Serggy10/15.-TFG-Thesis-Luminous-Road-Emergency-Panel/Entrega TFG/Presentacion TFG Panel Luminoso V2.pdf

PANEL LUMINOSO DE EMERGENCIA EN CARRETERA CONTROLADO POR PANTALLA TÁCTIL Y DE FORMA INALÁMBRICA SERGIO CARRASCO HERNÁNDEZ - IEIA

# PANEL LUMINOSO DE EMERGENCIA EN

# CARRETERA CONTROLADO POR PANTALLA

TÁCTIL Y DE FORMA INALÁMBRICA.

## Sergio Carrasco Hernández Grado en Ingeniería Electrónica Industrial y Automática

### Tutor: Luis Carlos Herrero de Lucas Departamento Tecnología Electrónica

### Universidad de Valladolid

POR PANTALLA TÁCTIL Y DE FORMA INALÁMBRICA SERGIO CARRASCO HERNÁNDEZ - IEIA

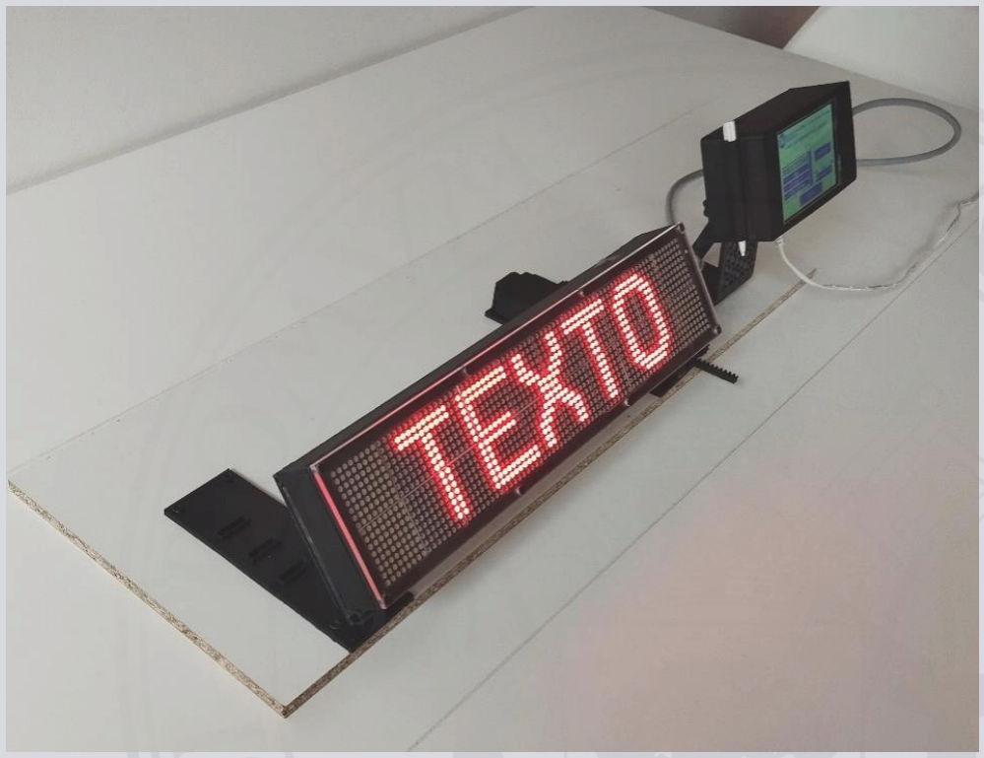
[picture p1: figure]

# ÍNDICE

1. ORIGEN DEL PROYECTO.
2. OBJETIVOS.
3. HARDWARE EMPLEADO.

# 4. PRUEBA DE LOS ELEMENTOS

5. FABRICACIÓN DEL PROTOTIPO.
6. PROGRAMACIÓN DEL PROTOTIPO.
7. RESUMEN DEL PROYECTO.
8. PLANES A FUTURO.

1. ORIGEN DEL PROYECTO.

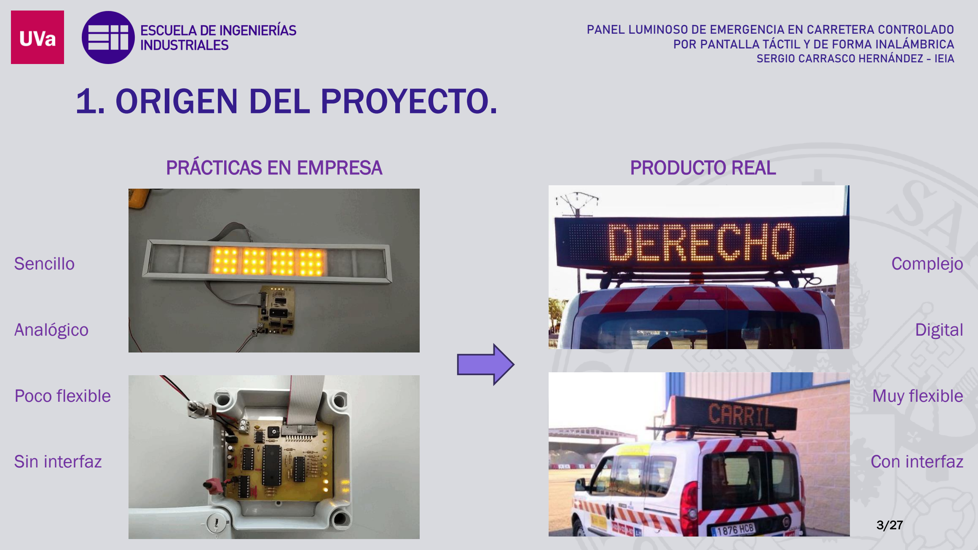
[picture p2: page 3]

POR PANTALLA TÁCTIL Y DE FORMA INALÁMBRICA SERGIO CARRASCO HERNÁNDEZ - IEIA

PRÁCTICAS EN EMPRESA | PRODUCTO REAL

## Sencillo

## Analógico

## Poco flexible

## Sin interfaz

## Complejo

## Digital

## Muy flexible

## Con interfaz

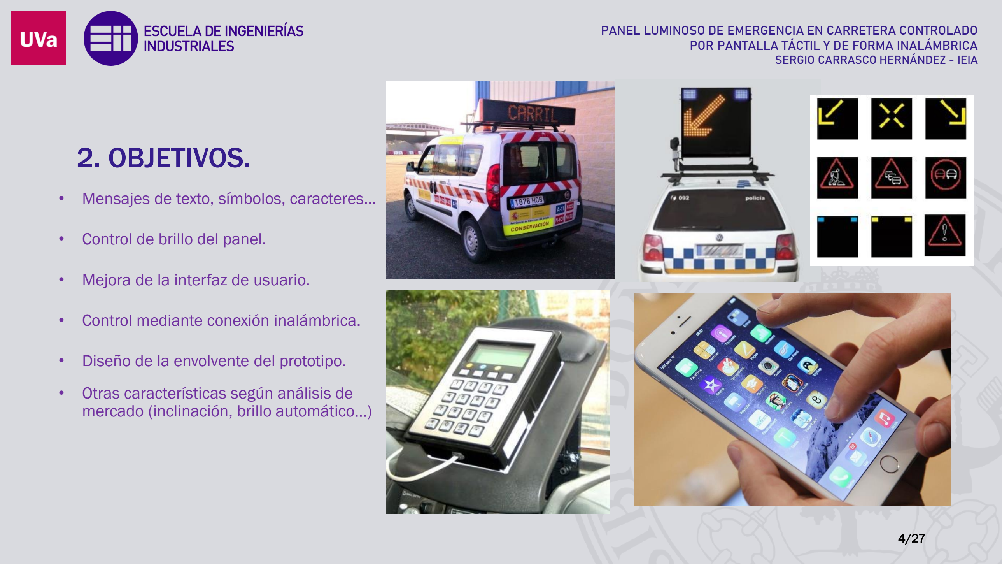
[picture p3: page 4]

POR PANTALLA TÁCTIL Y DE FORMA INALÁMBRICA SERGIO CARRASCO HERNÁNDEZ - IEIA

2. OBJETIVOS.
- Mensajes de texto, símbolos, caracteres…
- Control de brillo del panel.
- Mejora de la interfaz de usuario.
- Control mediante conexión inalámbrica.
- Diseño de la envolvente del prototipo.
- Otras características según análisis de mercado (inclinación, brillo automático…)

POR PANTALLA TÁCTIL Y DE FORMA INALÁMBRICA SERGIO CARRASCO HERNÁNDEZ - IEIA

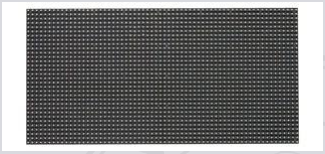
[picture p4: figure]

# 3. HARDWARE

EMPLEADO.

- 3.1. ALTERNATIVAS PARA EL PANEL LUMINOSO.

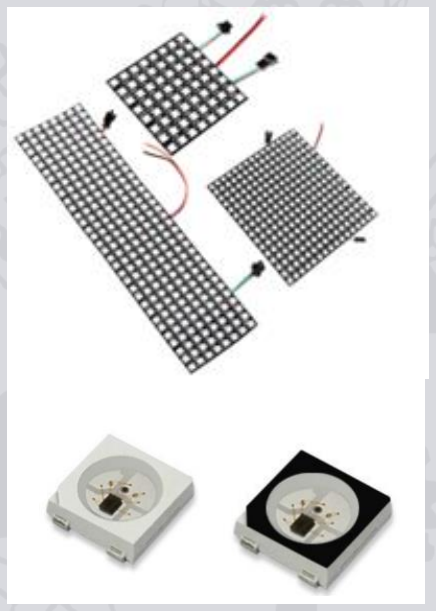
[picture p5: figure]

WS2812B | 5/27

LDM-6432

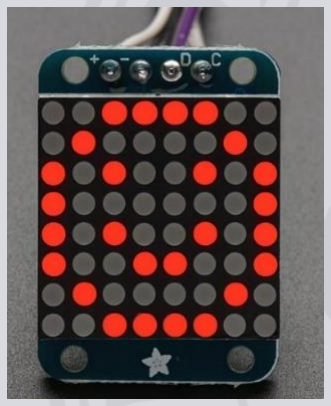
[picture p6: figure]

HT16K33
(I2C 8 DIRECCIONES)

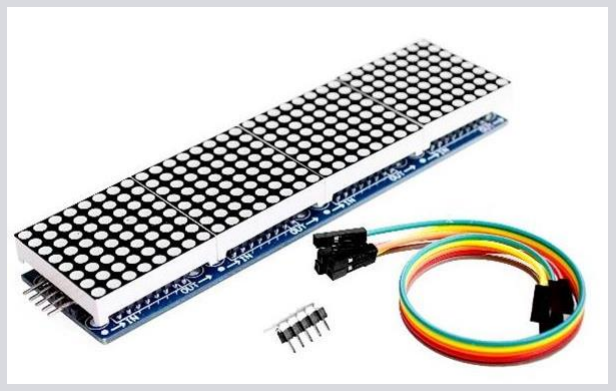
[picture p7: figure]

MAX7219/21
- Protocolo SPI.

## - Concatenación de multitud

de matrices.
- Memoria RAM.

## - Limitación de brillo de

forma externa.
- Alimentación a 5V.

# 3. HARDWARE

## PLACAS DE DESARROLLO

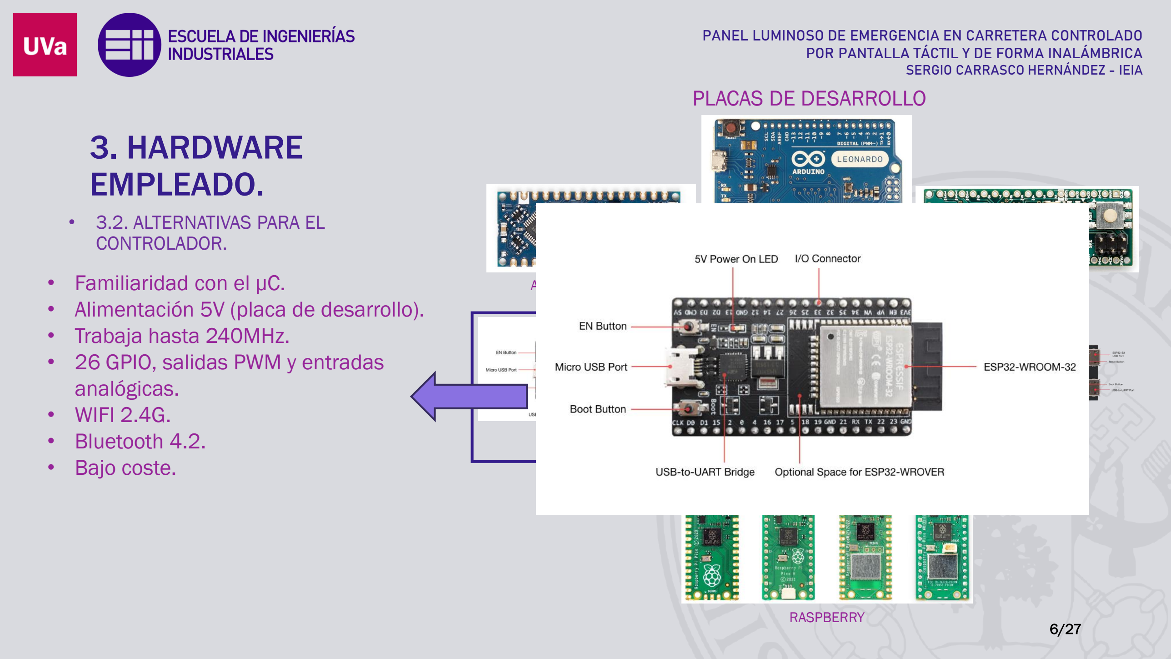
[picture p8: page 6]

POR PANTALLA TÁCTIL Y DE FORMA INALÁMBRICA SERGIO CARRASCO HERNÁNDEZ - IEIA

EMPLEADO.

- 3.2. ALTERNATIVAS PARA EL CONTROLADOR.
- Familiaridad con el µC.
- Alimentación 5V (placa de desarrollo).
- Trabaja hasta 240MHz.

## - 26 GPIO, salidas PWM y entradas

analógicas.
- WIFI 2.4G.
- Bluetooth 4.2.
- Bajo coste.

Arduino Nano Every
(ATMega4809)

Arduino Leonardo
(ATMega32u4)

Arduino Micro
(ATMega32u4)

ESP32 DEVKIT-C
(ESP32-WROOM)

ESP32-S2 DEVKIT-M-1
(ESP32-S2-MINI)

ESP32-S3-DEVKITC-1
(ESP32-S3-MINI)

RASPBERRY

POR PANTALLA TÁCTIL Y DE FORMA INALÁMBRICA SERGIO CARRASCO HERNÁNDEZ - IEIA

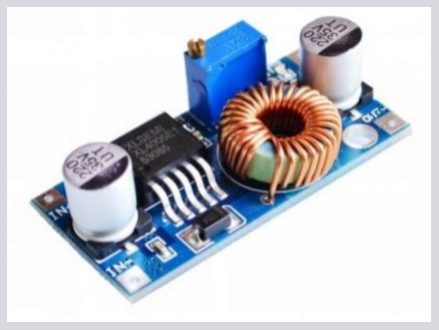
[picture p9: figure]

# 3. HARDWARE

EMPLEADO.

- 3.2. PERIFÉRICOS.

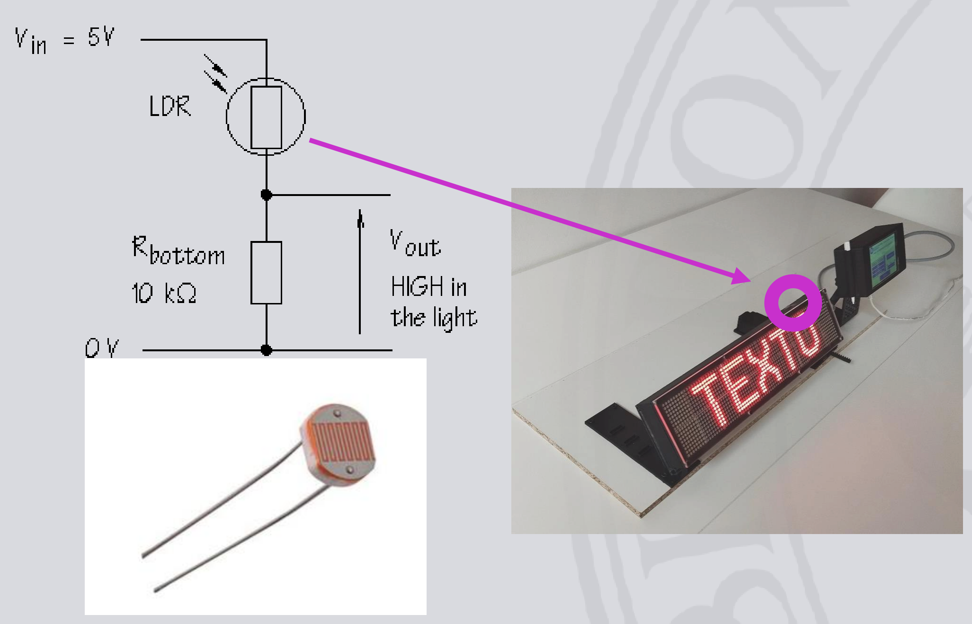
[picture p10: figure]
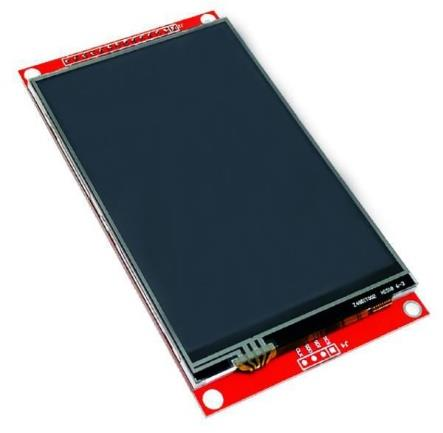
[picture p11: figure]
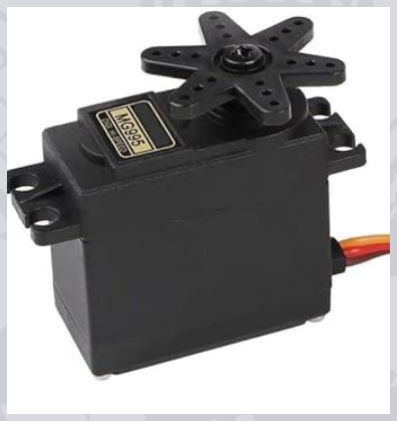
[picture p12: figure]

Pantalla táctil TFT SPI 480x320 píxeles | LDR | Servomotor MG995
INTERFAZ DE USUARIO | SENSOR DE NIVEL DE LUZ | SISTEMA PLEGADO

## ALIMENTACIÓN DEL DISPOSITVO

Convertidor CC-CC de 12V a 5V

# 4. PRUEBA DE LOS

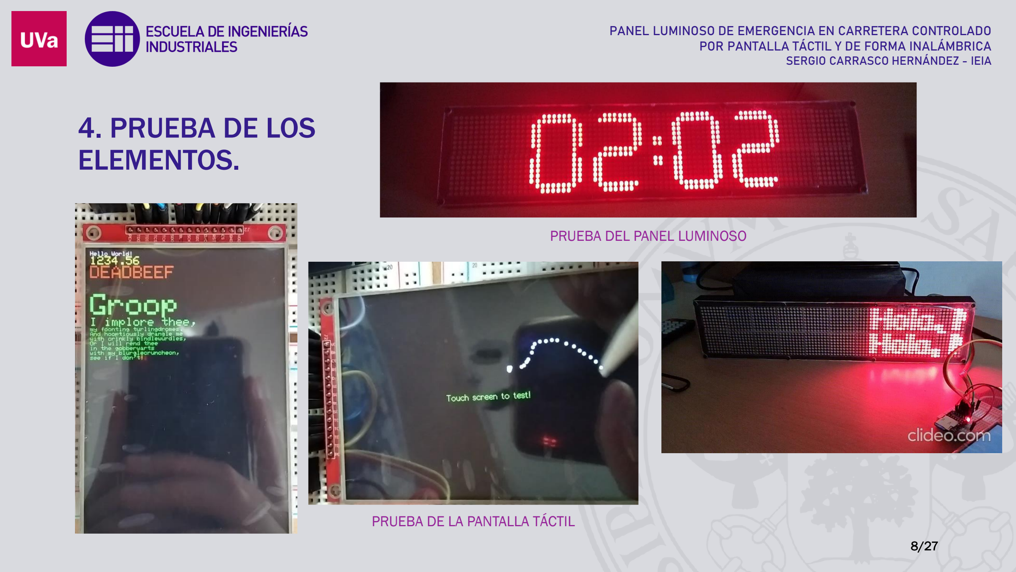
[picture p13: page 8]

POR PANTALLA TÁCTIL Y DE FORMA INALÁMBRICA SERGIO CARRASCO HERNÁNDEZ - IEIA

ELEMENTOS.

PRUEBA DEL PANEL LUMINOSO

PRUEBA DE LA PANTALLA TÁCTIL

# 5. FABRICACIÓN DEL

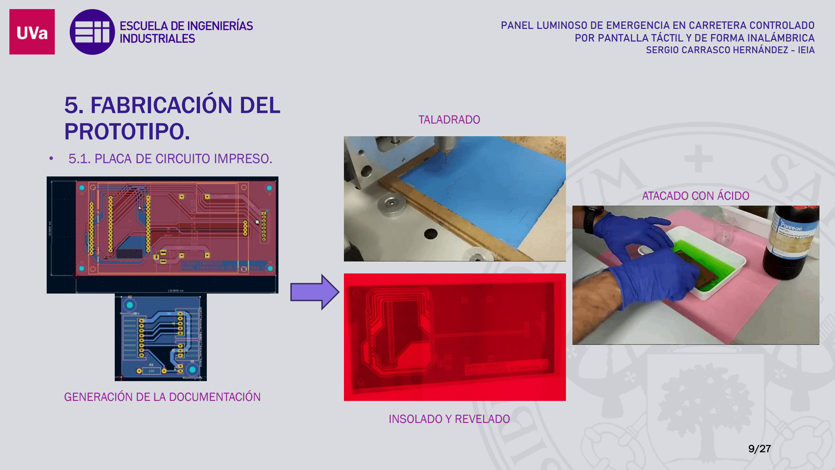
[picture p14: page 9]

POR PANTALLA TÁCTIL Y DE FORMA INALÁMBRICA SERGIO CARRASCO HERNÁNDEZ - IEIA

PROTOTIPO.

- 5.1. PLACA DE CIRCUITO IMPRESO.

GENERACIÓN DE LA DOCUMENTACIÓN

TALADRADO

INSOLADO Y REVELADO

ATACADO CON ÁCIDO

# 5. FABRICACIÓN DEL

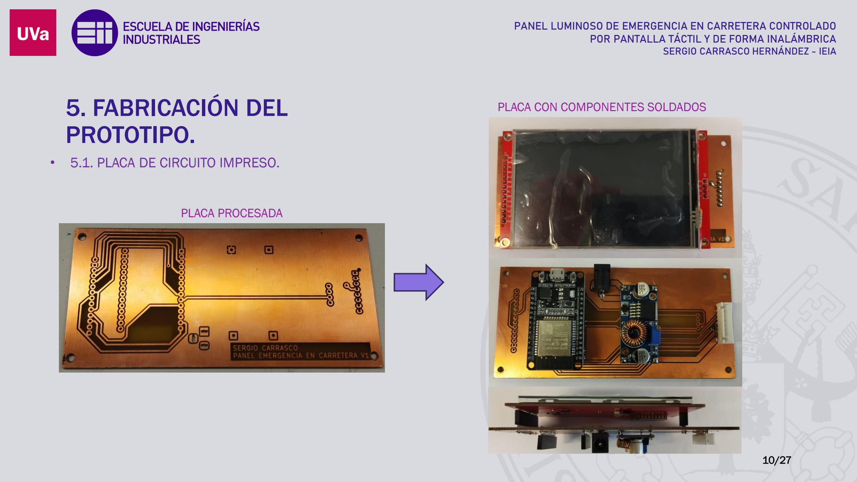
[picture p15: page 10]

POR PANTALLA TÁCTIL Y DE FORMA INALÁMBRICA SERGIO CARRASCO HERNÁNDEZ - IEIA

PROTOTIPO.

- 5.1. PLACA DE CIRCUITO IMPRESO.

PLACA PROCESADA

PLACA CON COMPONENTES SOLDADOS

# 5. FABRICACIÓN DEL

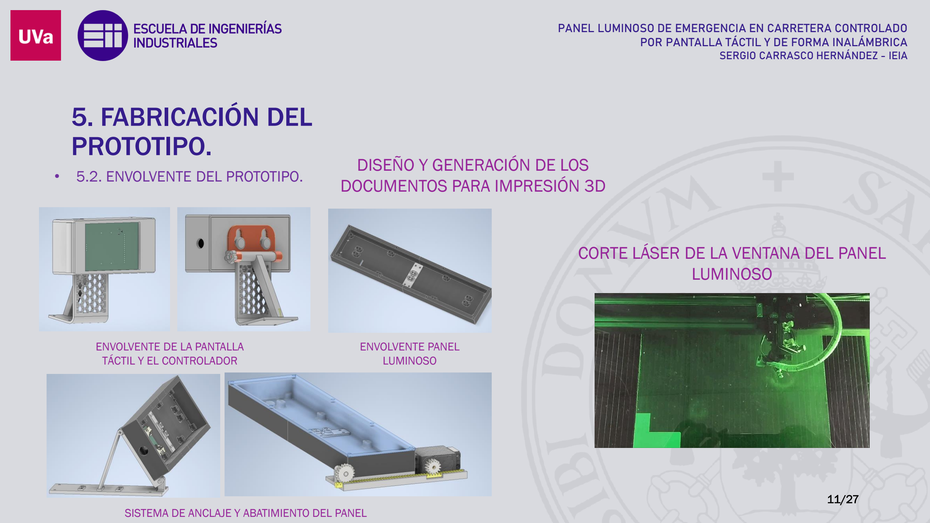
[picture p16: page 11]

POR PANTALLA TÁCTIL Y DE FORMA INALÁMBRICA SERGIO CARRASCO HERNÁNDEZ - IEIA

PROTOTIPO.

- 5.2. ENVOLVENTE DEL PROTOTIPO.

## DISEÑO Y GENERACIÓN DE LOS DOCUMENTOS PARA IMPRESIÓN 3D

ENVOLVENTE PANEL
LUMINOSO

ENVOLVENTE DE LA PANTALLA
TÁCTIL Y EL CONTROLADOR

SISTEMA DE ANCLAJE Y ABATIMIENTO DEL PANEL

## CORTE LÁSER DE LA VENTANA DEL PANEL LUMINOSO

# 5. FABRICACIÓN DEL

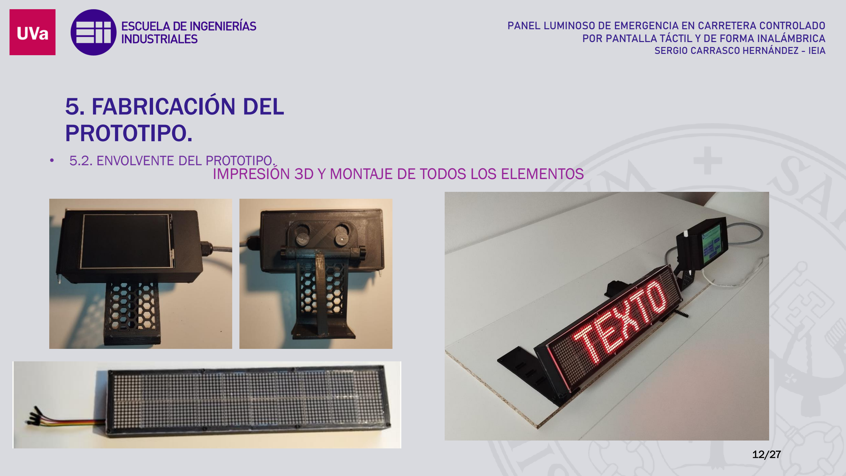
[picture p17: page 12]

POR PANTALLA TÁCTIL Y DE FORMA INALÁMBRICA SERGIO CARRASCO HERNÁNDEZ - IEIA

PROTOTIPO.

- 5.2. ENVOLVENTE DEL PROTOTIPO.

## IMPRESIÓN 3D Y MONTAJE DE TODOS LOS ELEMENTOS

POR PANTALLA TÁCTIL Y DE FORMA INALÁMBRICA SERGIO CARRASCO HERNÁNDEZ - IEIA

# 6. PROGRAMACIÓN DEL PROTOTIPO

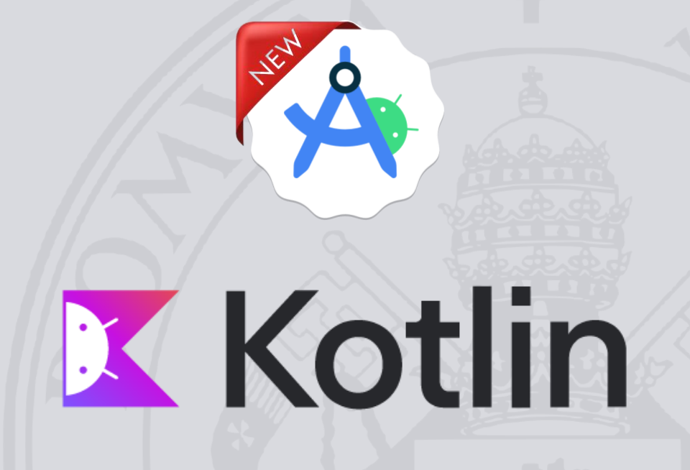
[picture p18: figure]
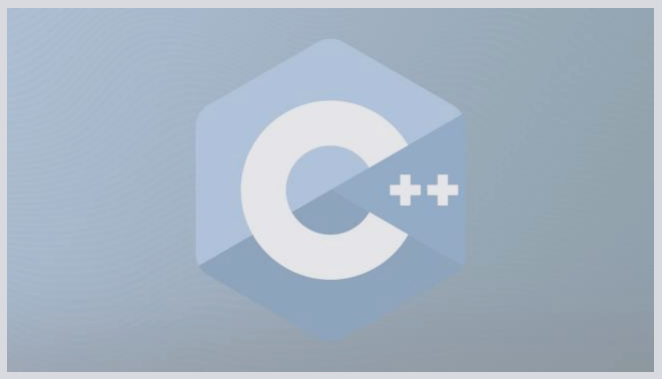
[picture p19: figure]

# 6. PROGRAMACIÓN DEL

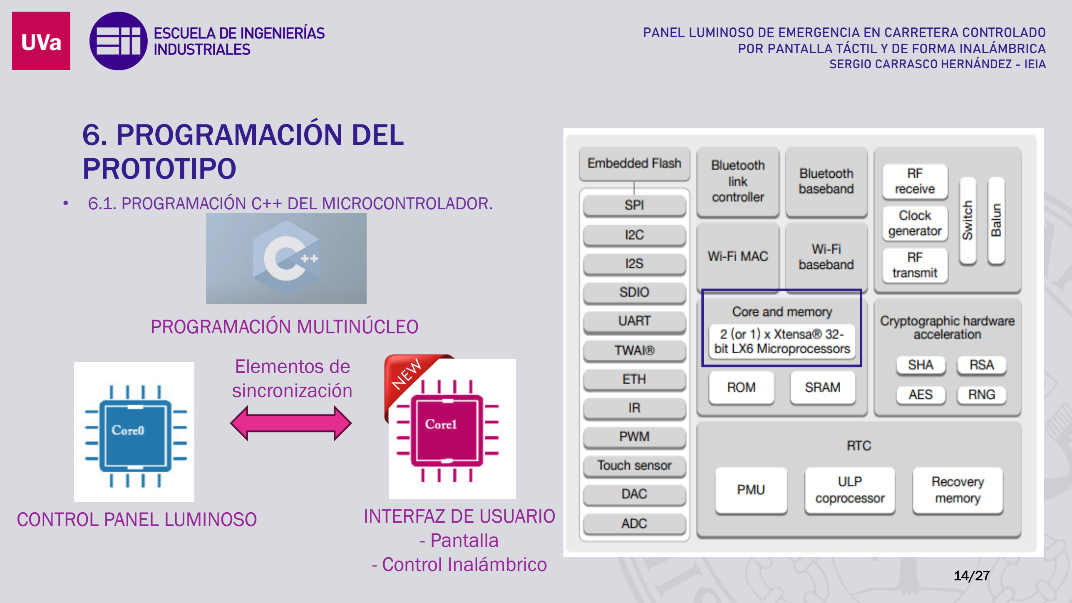
[picture p20: page 14]

POR PANTALLA TÁCTIL Y DE FORMA INALÁMBRICA SERGIO CARRASCO HERNÁNDEZ - IEIA

# PROTOTIPO

- 6.1. PROGRAMACIÓN C++ DEL MICROCONTROLADOR.

## PROGRAMACIÓN MULTINÚCLEO

CONTROL PANEL LUMINOSO | INTERFAZ DE USUARIO

## - Pantalla - Control Inalámbrico

## Elementos de sincronización

POR PANTALLA TÁCTIL Y DE FORMA INALÁMBRICA SERGIO CARRASCO HERNÁNDEZ - IEIA

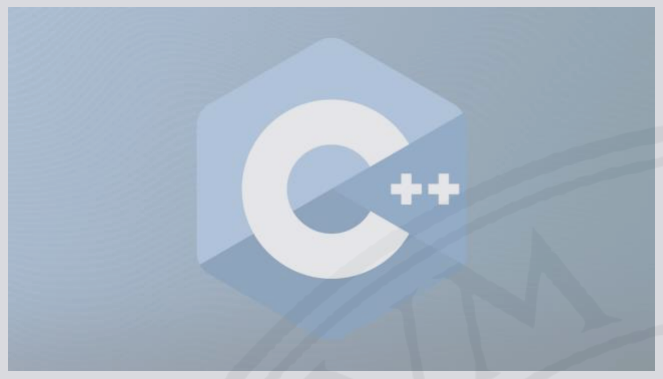
[picture p21: figure]

# 6. PROGRAMACIÓN DEL

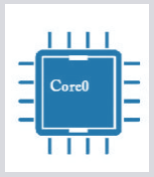
[picture p22: figure]

# PROTOTIPO

- 6.1. PROGRAMACIÓN C++ DEL MICROCONTROLADOR.

## NÚCLEO 0: PANEL LUMINOSO

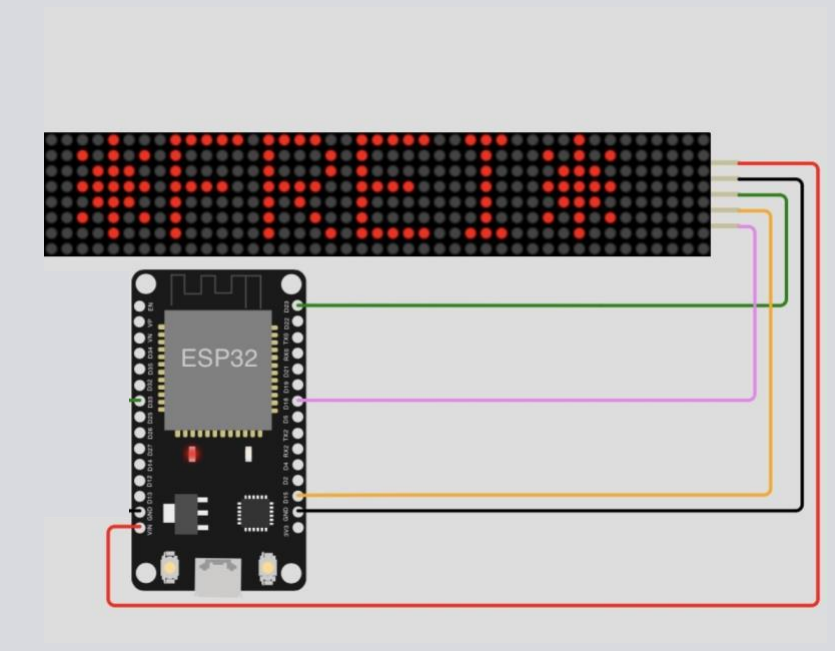
[picture p23: figure]

- Creación de librerías propias y modificación de las existentes.
- Creación de fuentes y caracteres especiales.
- Inclinación del panel mediante un servomotor.
- Ajuste automático del nivel de brillo mediante LDR.
- Guardado de parámetros de inclinación y brillo en SPIFFS.
- La gestión de los mensajes mediante máquina de estados.

# 6. PROGRAMACIÓN DEL

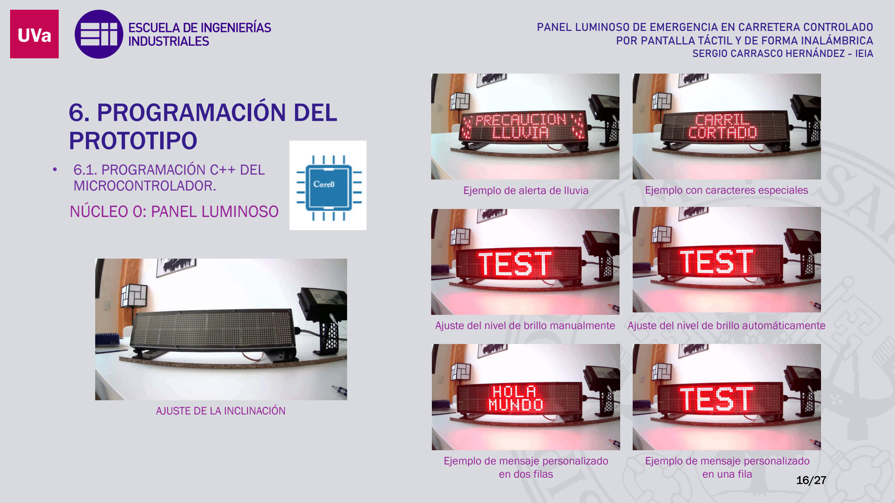
[picture p24: page 16]

POR PANTALLA TÁCTIL Y DE FORMA INALÁMBRICA SERGIO CARRASCO HERNÁNDEZ - IEIA

# PROTOTIPO

- 6.1. PROGRAMACIÓN C++ DEL MICROCONTROLADOR.

## NÚCLEO 0: PANEL LUMINOSO

AJUSTE DE LA INCLINACIÓN

Ajuste del nivel de brillo manualmente | Ajuste del nivel de brillo automáticamente
Ejemplo de alerta de lluvia | Ejemplo con caracteres especiales

Ejemplo de mensaje personalizado en dos filas

Ejemplo de mensaje personalizado en una fila

# 6. PROGRAMACIÓN DEL

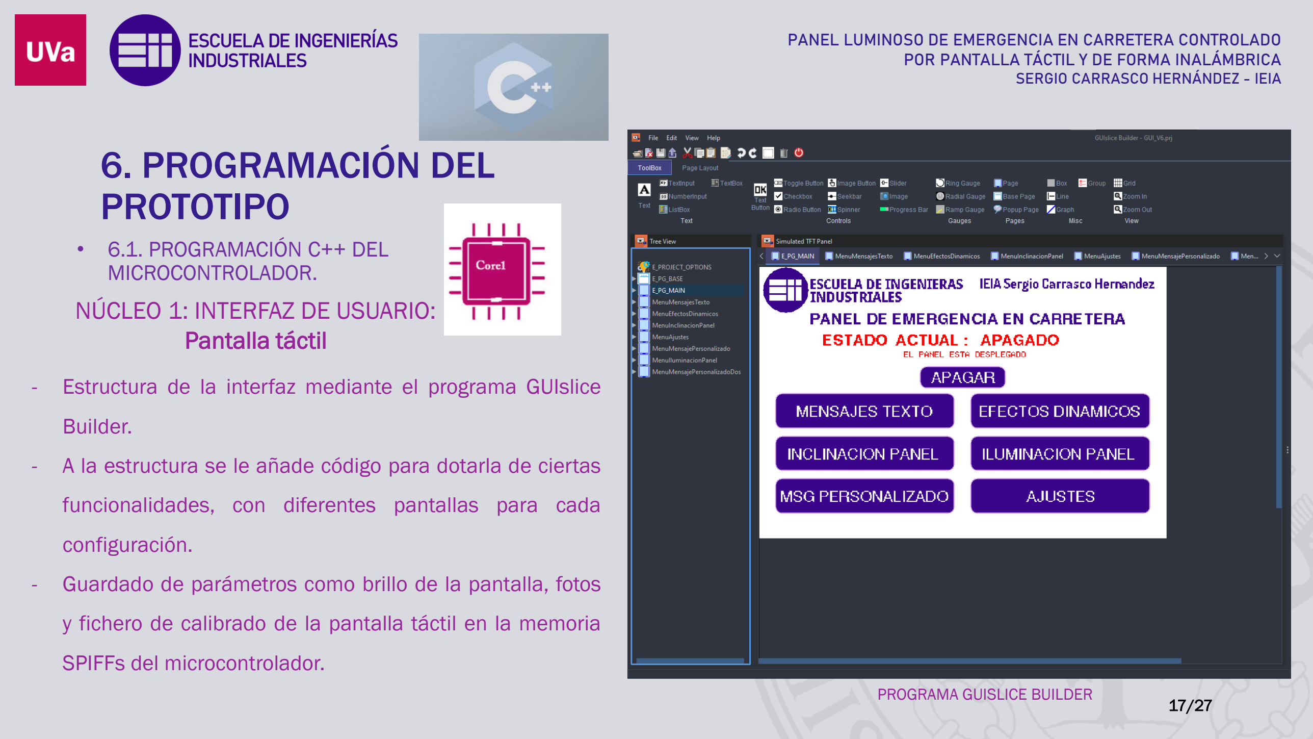
[picture p25: page 17]

POR PANTALLA TÁCTIL Y DE FORMA INALÁMBRICA SERGIO CARRASCO HERNÁNDEZ - IEIA

# PROTOTIPO

- 6.1. PROGRAMACIÓN C++ DEL MICROCONTROLADOR.

## NÚCLEO 1: INTERFAZ DE USUARIO: Pantalla táctil

PROGRAMA GUISLICE BUILDER

- Estructura de la interfaz mediante el programa GUIslice

Builder.

- A la estructura se le añade código para dotarla de ciertas

funcionalidades, con diferentes pantallas para cada

configuración.

- Guardado de parámetros como brillo de la pantalla, fotos

y fichero de calibrado de la pantalla táctil en la memoria

SPIFFs del microcontrolador.

# 6. PROGRAMACIÓN DEL

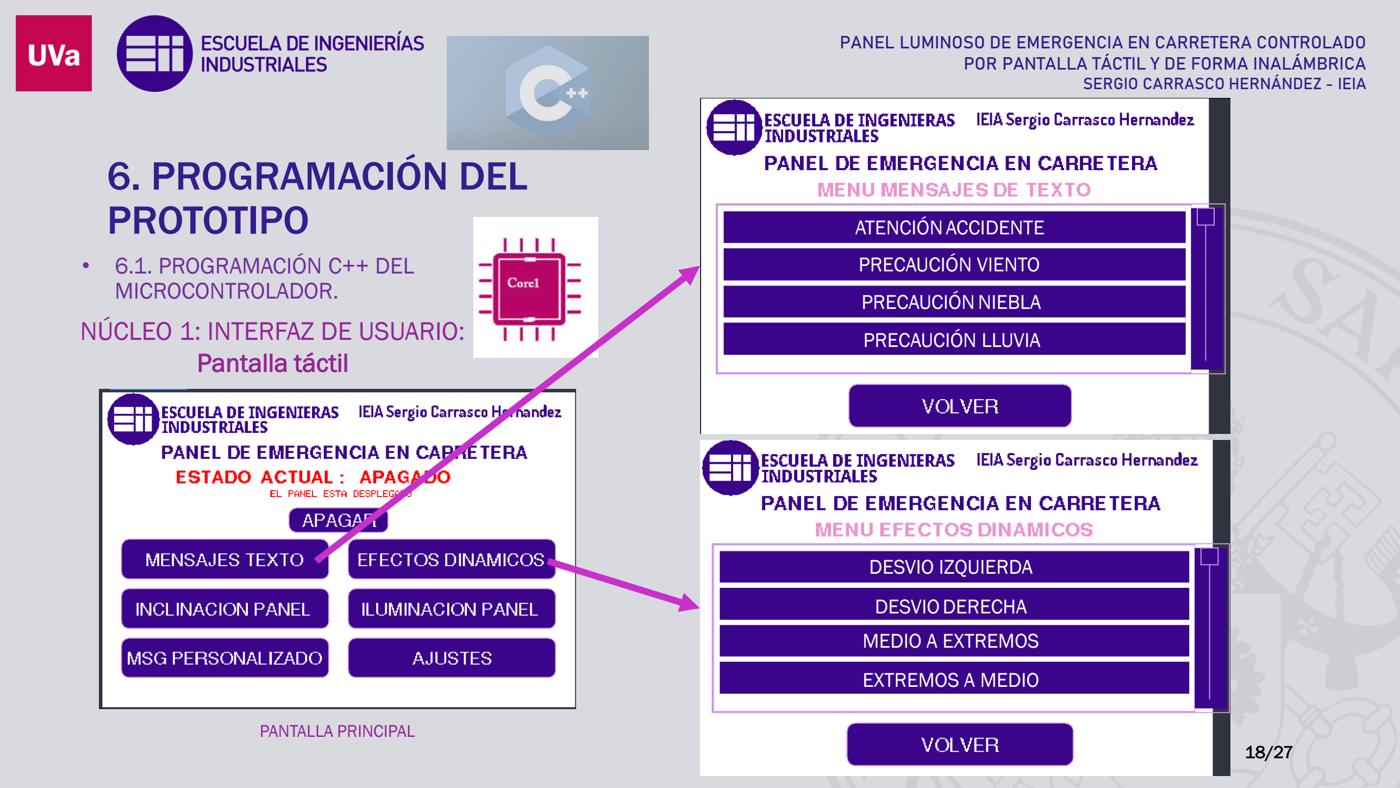
[picture p26: page 18]

POR PANTALLA TÁCTIL Y DE FORMA INALÁMBRICA SERGIO CARRASCO HERNÁNDEZ - IEIA

# PROTOTIPO

- 6.1. PROGRAMACIÓN C++ DEL MICROCONTROLADOR.

## NÚCLEO 1: INTERFAZ DE USUARIO: Pantalla táctil

PANTALLA PRINCIPAL

ATENCIÓNACCIDENTE

PRECAUCIÓN VIENTO

PRECAUCIÓNNIEBLA

PRECAUCIÓN LLUVIA

DESVIO IZQUIERDA

DESVIODERECHA

MEDIO A EXTREMOS

EXTREMOS A MEDIO

# 6. PROGRAMACIÓN DEL

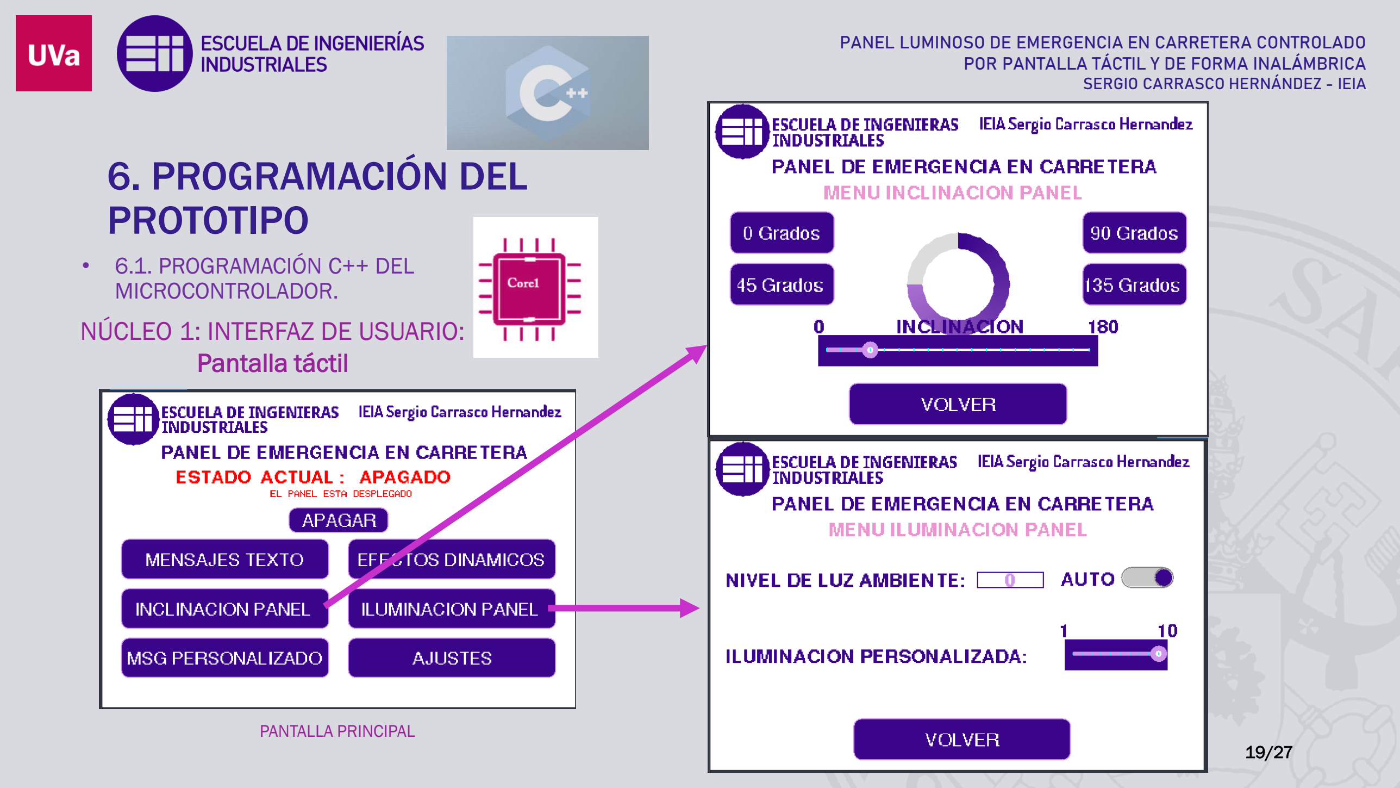
[picture p27: page 19]

POR PANTALLA TÁCTIL Y DE FORMA INALÁMBRICA SERGIO CARRASCO HERNÁNDEZ - IEIA

# PROTOTIPO

- 6.1. PROGRAMACIÓN C++ DEL MICROCONTROLADOR.

## NÚCLEO 1: INTERFAZ DE USUARIO: Pantalla táctil

PANTALLA PRINCIPAL

# 6. PROGRAMACIÓN DEL

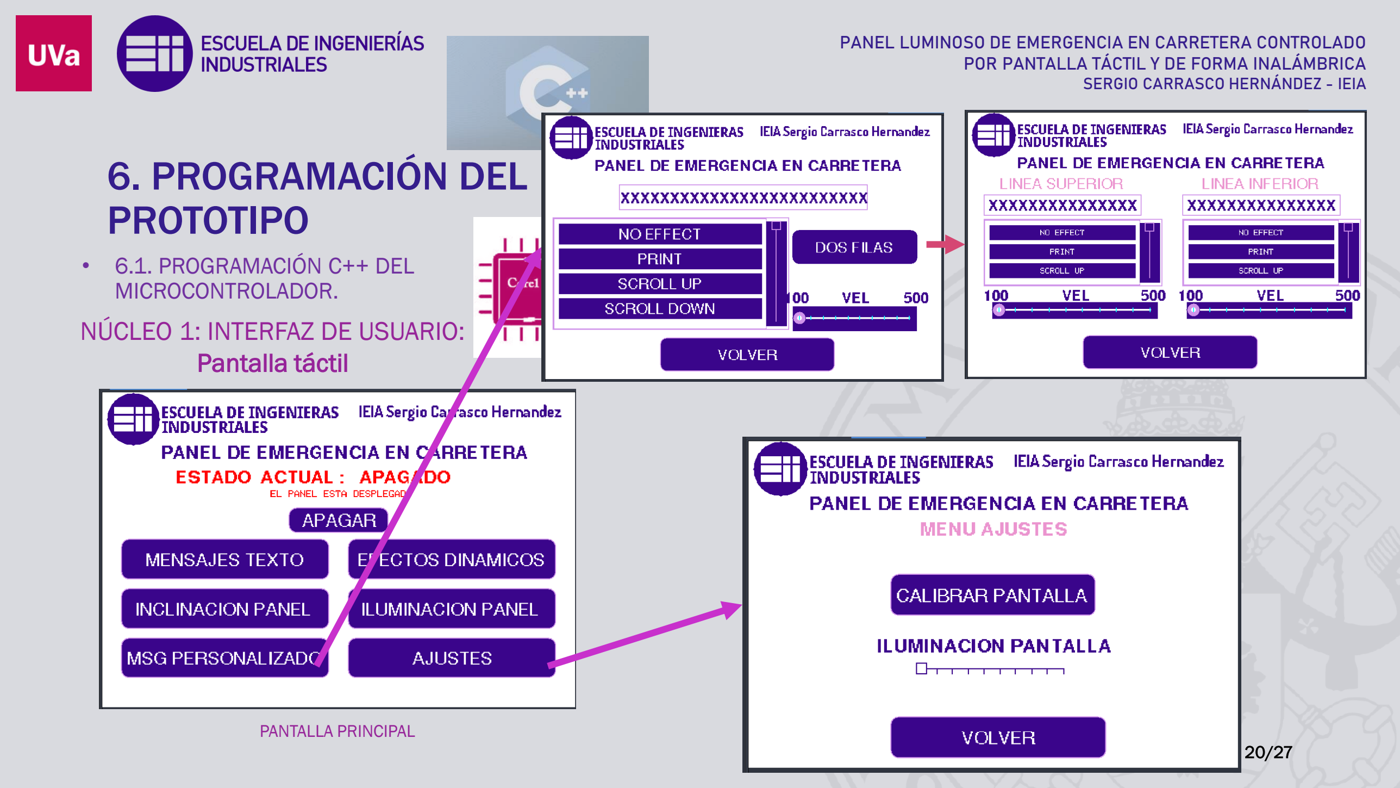
[picture p28: page 20]

POR PANTALLA TÁCTIL Y DE FORMA INALÁMBRICA SERGIO CARRASCO HERNÁNDEZ - IEIA

# PROTOTIPO

- 6.1. PROGRAMACIÓN C++ DEL MICROCONTROLADOR.

## NÚCLEO 1: INTERFAZ DE USUARIO: Pantalla táctil

PANTALLA PRINCIPAL

# 6. PROGRAMACIÓN DEL

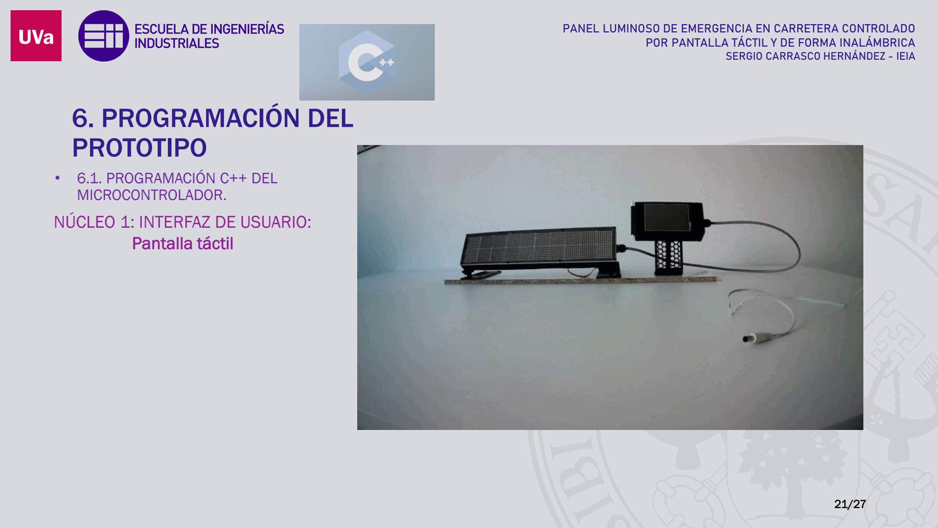
[picture p29: page 21]

POR PANTALLA TÁCTIL Y DE FORMA INALÁMBRICA SERGIO CARRASCO HERNÁNDEZ - IEIA

# PROTOTIPO

- 6.1. PROGRAMACIÓN C++ DEL MICROCONTROLADOR.

## NÚCLEO 1: INTERFAZ DE USUARIO: Pantalla táctil

Video

# 6. PROGRAMACIÓN DEL

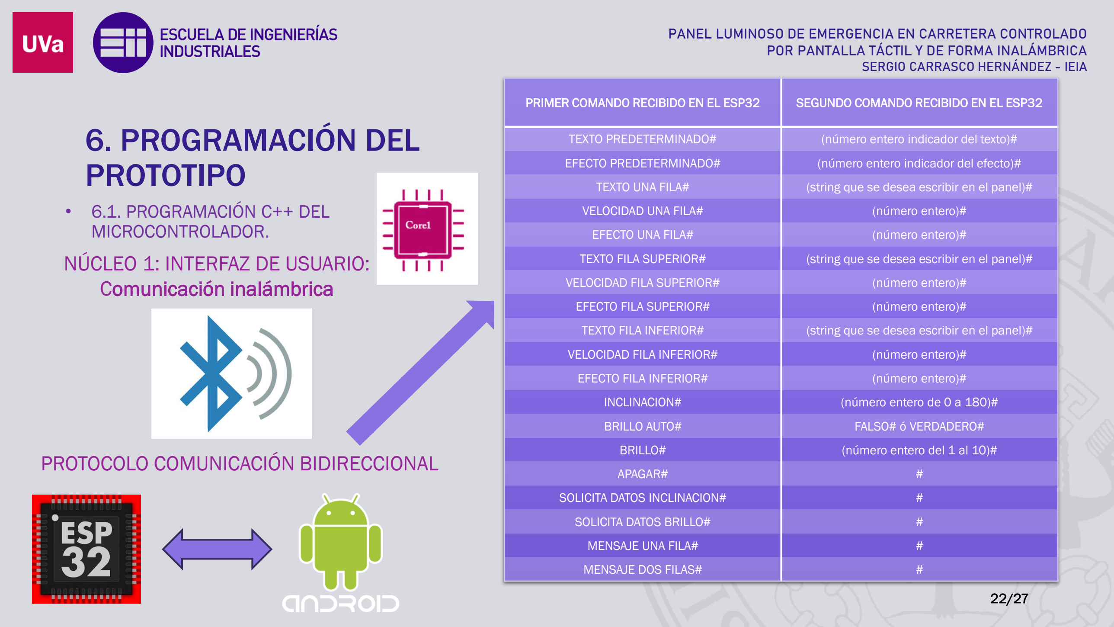
[picture p30: page 22]

POR PANTALLA TÁCTIL Y DE FORMA INALÁMBRICA SERGIO CARRASCO HERNÁNDEZ - IEIA

PRIMER COMANDO RECIBIDO EN EL ESP32 | SEGUNDO COMANDO RECIBIDO EN EL ESP32
TEXTO PREDETERMINADO# | (número entero indicador del texto)#
EFECTO PREDETERMINADO# | (número entero indicador del efecto)#
TEXTO UNA FILA# | (string que se desea escribir en el panel)#
VELOCIDAD UNA FILA# | (número entero)#
EFECTO UNA FILA# | (número entero)#
TEXTO FILA SUPERIOR# | (string que se desea escribir en el panel)#
VELOCIDAD FILA SUPERIOR# | (número entero)#
EFECTO FILA SUPERIOR# | (número entero)#
TEXTO FILA INFERIOR# | (string que se desea escribir en el panel)#
VELOCIDAD FILA INFERIOR# | (número entero)#
EFECTO FILA INFERIOR# | (número entero)#
INCLINACION# | (número entero de 0 a 180)#
BRILLO AUTO# | FALSO# ó VERDADERO#
BRILLO# | (número entero del 1 al 10)#
APAGAR# | #
SOLICITA DATOS INCLINACION# | #
SOLICITA DATOS BRILLO# | #
MENSAJE UNA FILA# | #
MENSAJE DOS FILAS# | #

# PROTOTIPO

- 6.1. PROGRAMACIÓN C++ DEL MICROCONTROLADOR.

## NÚCLEO 1: INTERFAZ DE USUARIO: Comunicación inalámbrica

## PROTOCOLO COMUNICACIÓN BIDIRECCIONAL

# 6. PROGRAMACIÓN DEL

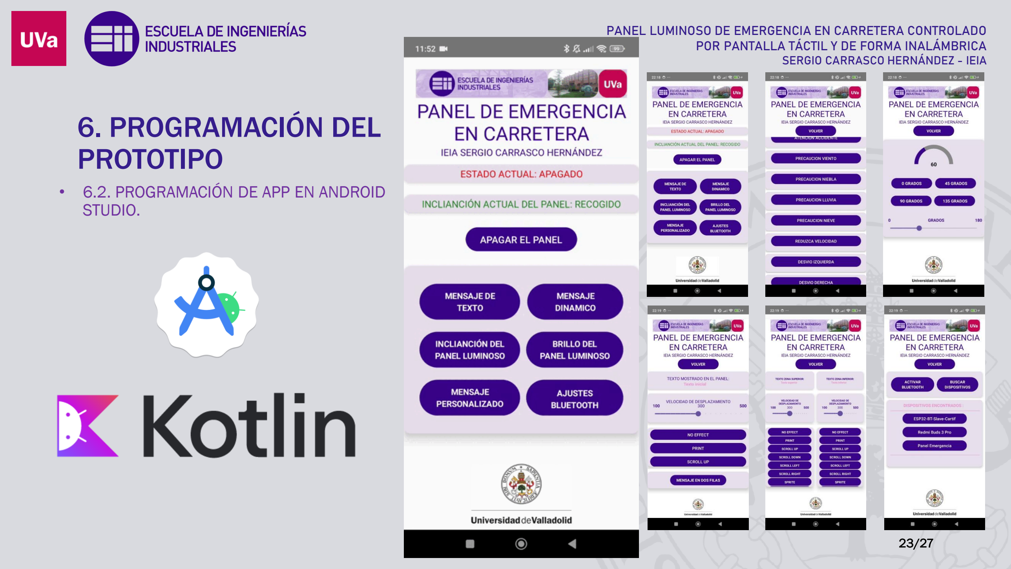
[picture p31: page 23]

POR PANTALLA TÁCTIL Y DE FORMA INALÁMBRICA SERGIO CARRASCO HERNÁNDEZ - IEIA

# PROTOTIPO

- 6.2. PROGRAMACIÓN DE APP EN ANDROID STUDIO.

# 6. PROGRAMACIÓN DEL

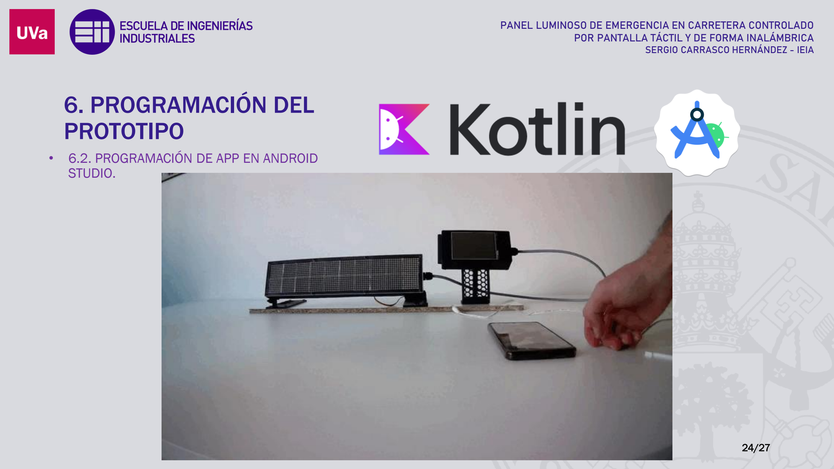
[picture p32: page 24]

POR PANTALLA TÁCTIL Y DE FORMA INALÁMBRICA SERGIO CARRASCO HERNÁNDEZ - IEIA

# PROTOTIPO

- 6.2. PROGRAMACIÓN DE APP EN ANDROID STUDIO.

POR PANTALLA TÁCTIL Y DE FORMA INALÁMBRICA SERGIO CARRASCO HERNÁNDEZ - IEIA

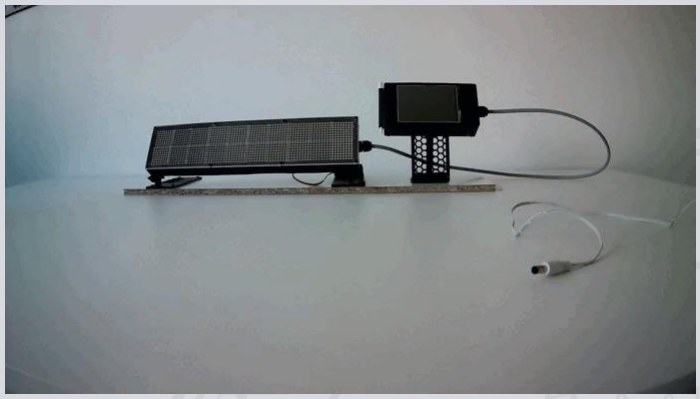
[picture p33: figure]

# 7. RESUMEN DEL

PROYECTO.

✓ Cumplimiento de objetivos:

✓ | Mensajes de texto.
✓ | Mensajes más complejos.
✓ | Mejora de la interfaz de usuario.
✓ | Control de luminosidad.
✓ | Panel plegable.
✓ | Comunicación inalámbrica por Bluetooth.

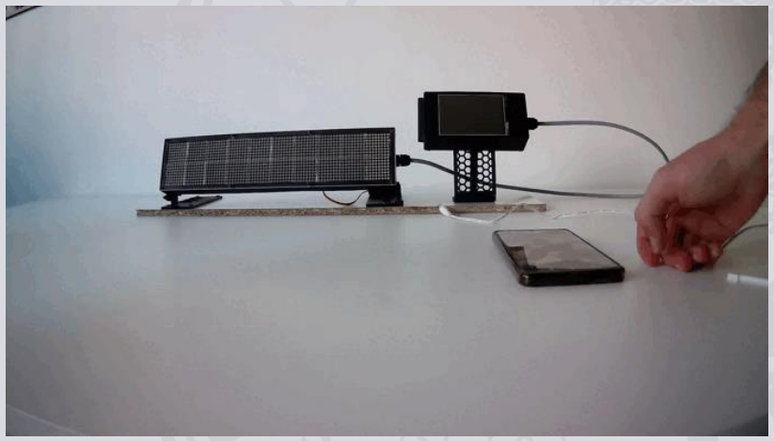
[picture p34: figure]

✓ Diseño y fabricación de la PCB.

✓ Diseño y fabricación de la envolvente.

✓ Programación multinúcleo.

✓ Programación de una aplicación Android desde cero.

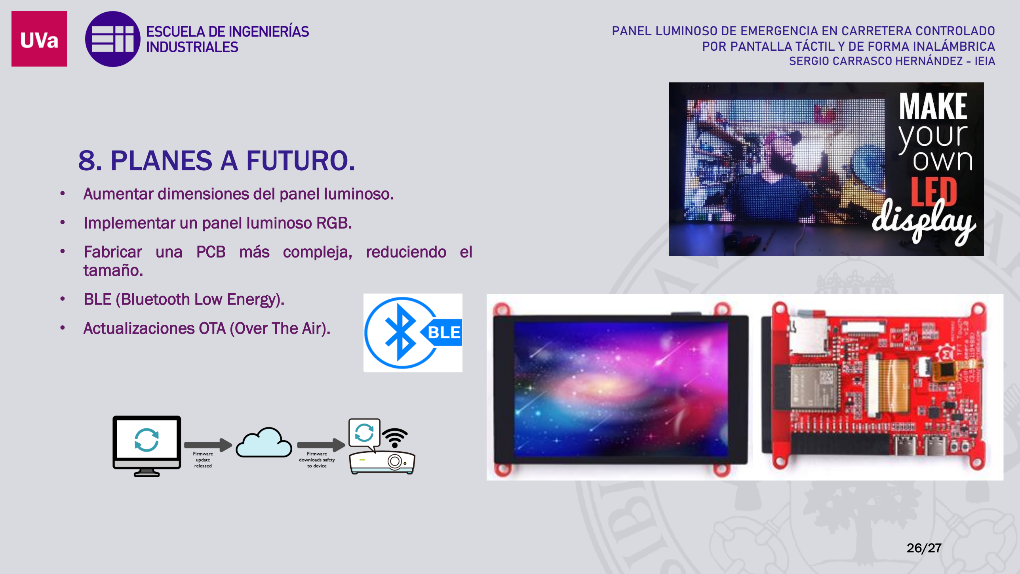
[picture p35: page 26]

POR PANTALLA TÁCTIL Y DE FORMA INALÁMBRICA SERGIO CARRASCO HERNÁNDEZ - IEIA

8. PLANES A FUTURO.
- Aumentar dimensiones del panel luminoso.
- Implementar un panel luminoso RGB.
- Fabricar una PCB más compleja, reduciendo el tamaño.
- BLE (Bluetooth Low Energy).
- Actualizaciones OTA (Over The Air).

POR PANTALLA TÁCTIL Y DE FORMA INALÁMBRICA SERGIO CARRASCO HERNÁNDEZ - IEIA

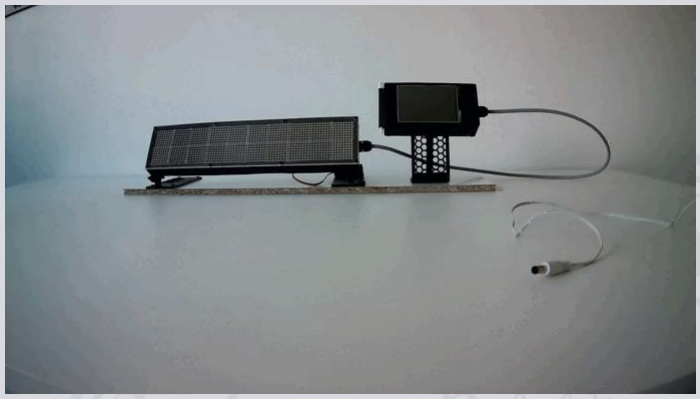
[picture p36: figure]

# CUESTIONES O PREGUNTAS

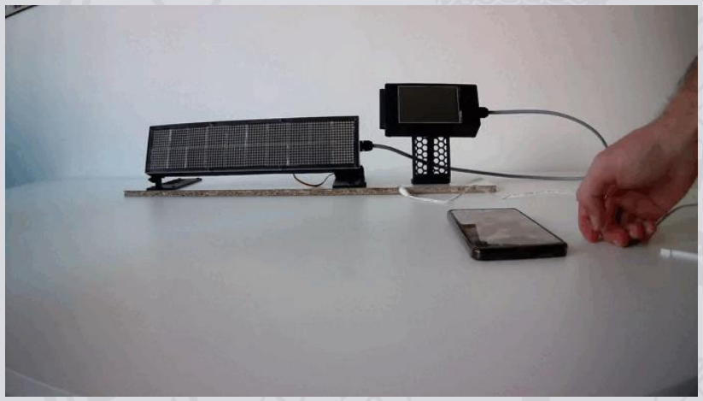
[picture p37: figure]

## GRACIAS POR SU ATENCIÓN
