Serggy10/15.-TFG-Thesis-Luminous-Road-Emergency-Panel/Entrega TFG/Anexos/4. Ficheros 3D/BaseSoporte.stl

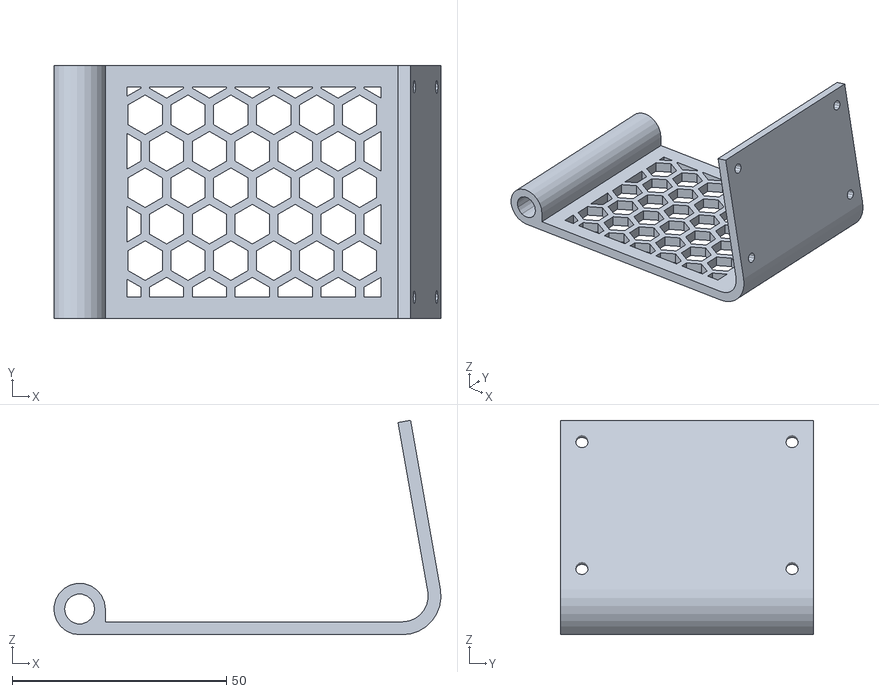
[picture p57: CAD file, 2025-03-06]
Entrega TFG/Anexos/4. Ficheros 3D/BaseSoporte.stl
90.2 x 59.0 x 50.0
