Serggy10/15.-TFG-Thesis-Luminous-Road-Emergency-Panel/Entrega TFG/Anexos/4. Ficheros 3D/Tirante.stl

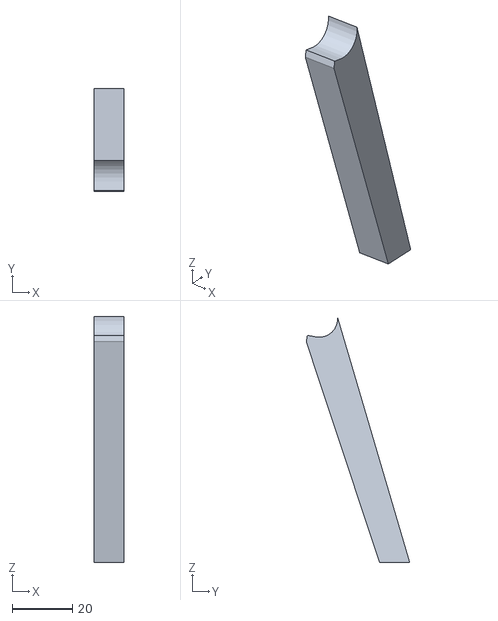
[picture p58: CAD file, 2025-03-06]
Entrega TFG/Anexos/4. Ficheros 3D/Tirante.stl
10.0 x 34.3 x 81.5
