Serggy10/15.-TFG-Thesis-Luminous-Road-Emergency-Panel/Entrega TFG/Anexos/4. Ficheros 3D/BisagraIzquierda.stl

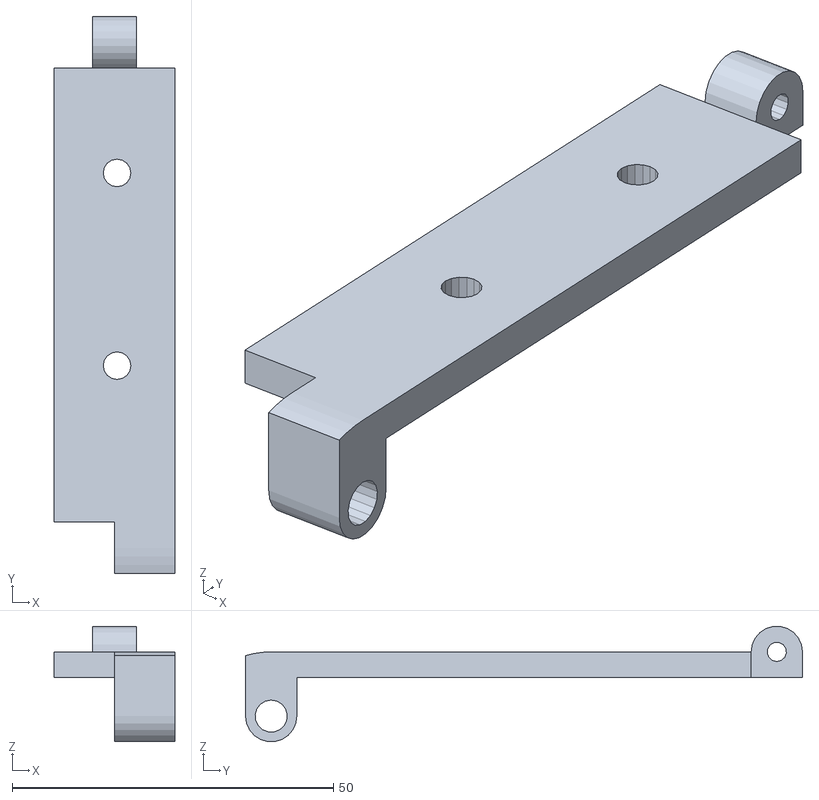
[picture p59: CAD file, 2025-03-06]
Entrega TFG/Anexos/4. Ficheros 3D/BisagraIzquierda.stl
18.8 x 86.7 x 17.9
