Serggy10/15.-TFG-Thesis-Luminous-Road-Emergency-Panel/Entrega TFG/Anexos/4. Ficheros 3D/Base.stl

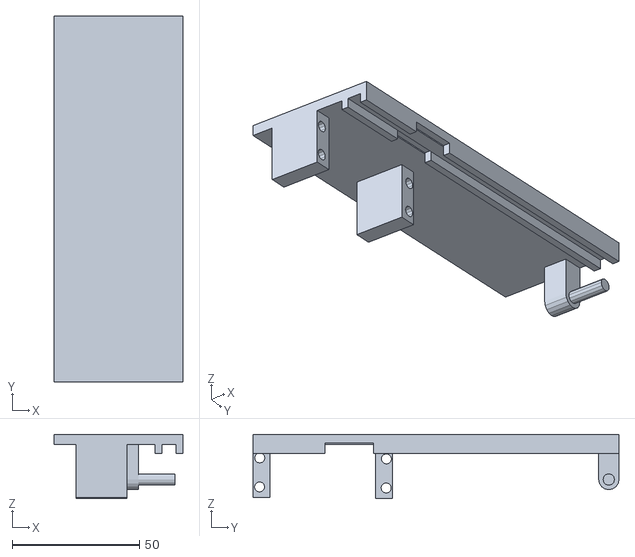
[picture p60: CAD file, 2025-03-06]
Entrega TFG/Anexos/4. Ficheros 3D/Base.stl
50.5 x 143.7 x 25.3
