Serggy10/15.-TFG-Thesis-Luminous-Road-Emergency-Panel/Entrega TFG/Anexos/4. Ficheros 3D/Tapa Transparente.stl

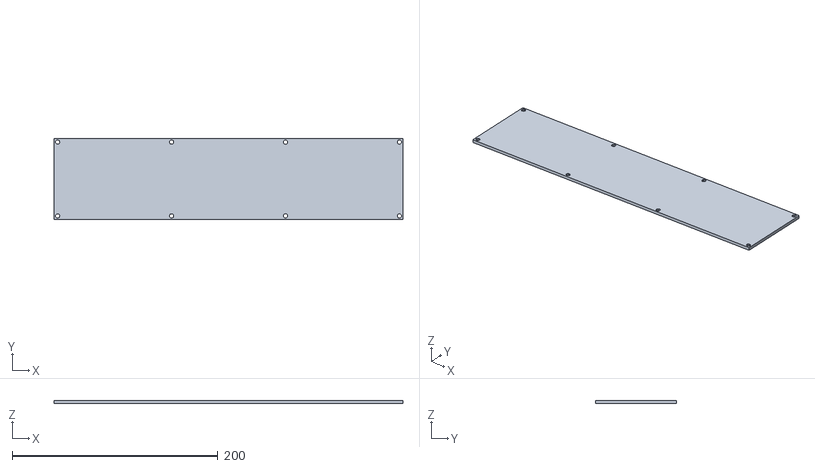
[picture p61: CAD file, 2025-03-06]
Entrega TFG/Anexos/4. Ficheros 3D/Tapa Transparente.stl
339.0 x 78.7 x 3.00
